linse/propinquity/software/data/hud/innerBoundaryMedium.png

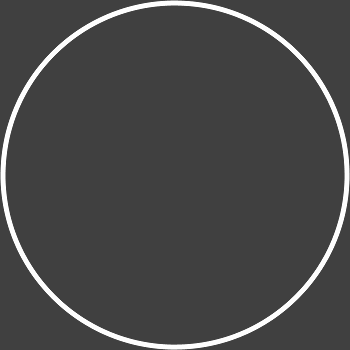
software/data/hud/innerBoundaryMedium.png
