linse/propinquity/software/processing/refactored/Propinquity/XPan.pde

// xbee personal area network of one local and up to two remote xbees

public class XPan { 
  
  //length (bytes) of incoming packet for proximity readings
  static final int PROX_IN_PACKET_LENGTH = 6; 
  //length (bytes) of outgoing packet for proximity steps
  static final int PROX_OUT_PACKET_LENGTH = 5; 
  
  static final int BROADCAST_ADDR = 0xFFFF; 

  static final int PROX_OUT_PACKET_TYPE = 1;
  static final int PROX_IN_PACKET_TYPE  = 2;
  static final int VIBE_OUT_PACKET_TYPE = 3;
  
  PApplet parent;
  XBeeReader xbee;

  public XPan(XBeeReader xbee, PApplet parent) {
    this.parent = parent;
    this.xbee = xbee;
    xbee.startXBee();
  }
  
  public XPan(Serial port, PApplet parent) {
    this.parent = parent;
    xbee = new XBeeReader(parent, port);
    xbee.startXBee();
  }
  
  void nodeDiscover() { 
    xbee.nodeDiscover();
    //xbee.sendAsynchronous(new AtCommand("ND"));
  }
  
  void stop() { 
    xbee.stopXBee(); 
  }
  
  void broadcastVibe(int value) { 
    broadcast(getVibePacket(value)); 
  }
  
  void broadcast(int[] data) {
    sendOutgoing(BROADCAST_ADDR, data);
  }
  
  void sendOutgoing(int adl, int[] data) {
     xbee.sendDataString16(adl, data);
  }
  
  private int[] getVibePacket(int value) {
    int[] packet = { VIBE_OUT_PACKET_TYPE, value };
    return packet;
  }
  
}
