linse/propinquity/software/processing/helpers/ScanTest/ScanTest.pde

import processing.serial.*;
import xbee.*;

XBeeManager xbeeManager;

void setup() {
  xbeeManager = new XBeeManager(this);
}

void draw() {
}

// hand over xbee events to xbee manager
void xBeeEvent(XBeeReader xbee) {
  xbeeManager.xBeeEvent(xbee);
}
